pavelkejik/chicken-feeder/src/pin_map.h

/***********************************************************************
 * Filename: pin_map.h
 * Author: Pavel Kejik
 * Date: 2024-04-12
 * Description:
 *     Defines pin mappings for various components like 
 *     motor control, buttons and sensors.
 *
 ***********************************************************************/

#pragma once

#define MOT_A1 7
#define MOT_A2 5
#define MOT_SLEEP 10
#define MOT_ISENSE 2
#define BTN_1 8
#define BTN_2 9
#define BTN_WAKE 0
#define LED_R 18
#define LBO 1
#define PDCLK 6
#define PDO 4
#define BAT_AINP 3
#define BAT_NSENSE 19
