pavelkejik/chicken-feeder/src/led.cpp

/***********************************************************************
 * Filename: led.cpp
 * Author: Pavel Kejik
 * Date: 2024-04-12
 *
 ***********************************************************************/

#include "led.h"

const uint8_t Led::dim_table[] = {0, 0, 16, 48, 64, 120, 180, 200, 220, 220, 200, 180, 120, 64, 48, 16, 0, 0};
