pavelkejik/chicken-feeder/src/weight.cpp

/***********************************************************************
 * Filename: weight.cpp
 * Author: Pavel Kejik
 * Date: 2024-04-12
 * 
 ***********************************************************************/


#include "weight.h"

RTC_DATA_ATTR uint32_t Weight::weightCnt = 0;
